RickP/MC5000_DevKit/gui/serialcommunication.h

#ifndef SERIALCOMMUNICATION_H
#define SERIALCOMMUNICATION_H

#include <QSerialPort>
#include <QTimer>
#include <QObject>
#include <QDebug>
#include <QMap>

class SerialCommunication : public QObject {
Q_OBJECT

Q_PROPERTY(int mcuConnections READ mcuConnections NOTIFY mcuConnectionChanged)
Q_PROPERTY(QStringList serialports READ serialports NOTIFY serialportsChanged)
Q_PROPERTY(QString errorMessage READ errorMessage NOTIFY errorMessageChanged)
Q_PROPERTY(QList<int> accRegisters READ accRegisters NOTIFY accRegistersChanged)
Q_PROPERTY(QList<int> datRegisters READ datRegisters NOTIFY datRegistersChanged)
Q_PROPERTY(QList<bool> isProgrammed READ isProgrammed NOTIFY isProgrammedChanged)

const QString LABEL_MARKER = ":";
const QString COMMENT_MARKER = "#";
const char LABEL_HEXCODE = 0x10 << 2;
const char START_CHAR = 0x7F;
const char END_CHAR = 0x7E;
const int SERIAL_DELAY = 8;
const int UPLOAD_RETRIES = 15;
const int MAX_PROGRAM_LENGTH = 74;

public:
explicit SerialCommunication(QObject *parent = nullptr);
~SerialCommunication();
int mcuConnections() const;
QStringList serialports();
QString errorMessage();
QList<int> datRegisters();
QList<int> accRegisters();
QList<bool> isProgrammed();

public slots:         // slots are public methods available in QML
void connectPort(QString port);
void updateRegisters();
void startUpload(QStringList codeList);
void loadPorts();
void readData();

signals:
void mcuConnectionChanged();
void errorMessageChanged();
void serialportsChanged();
void accRegistersChanged();
void datRegistersChanged();
void isProgrammedChanged();

private:
const int m_serialBaudRate = 19200;
QTimer *m_uploadTimeout;
QSerialPort *m_serial = nullptr;
int m_mcuConnections = 0;
int m_tries[3] = {0};
QString m_errorMessage = "";
QStringList m_serialports = {};
QStringList m_codeList = {};
QList<int> m_datRegisters = {0,0,0,0,0};
QList<int> m_accRegisters = {0,0,0,0,0};
QList<bool> m_isProgrammed = {false, false, false, false};
QList<bool> m_uploadDone = {true, true, true, true};
char encode8BitVal(QString);
char* encode16BitVal(QString);
void writeSerialByte(char, bool debug=false);
void upload(int mcuNum = 0);
void checkUpload();


const QMap<QString, char> registerEncodings = {
    {"x0", 0x40},
    {"x1", 0x48},
    {"p0", 0x50},
    {"p1", 0x58},
    {"dat", 0x60},
    {"acc", 0x70}
};

const QMap<QString, QPair<uint8_t, QStringList>> commands = {
    {
        "nop", {
            0x01 << 2, {}
        }
    },
    {
        "mov", {
            0x02 << 2, {"ri", "r"}
        }
    },
    {
        "jmp", {
            0x03 << 2, {"l"}
        },
    },
    {
        "slp", {
            0x04 << 2, {"ri"}
        },
    },
    {
        "slx", {
            0x05 << 2, {"r"}
        },
    },
    {
        "teq", {
            0x06 << 2, {"ri", "ri"}
        },
    },
    {
        "tgt", {
            0x07 << 2, {"ri", "ri"}
        },
    },
    {
        "tlt", {
            0x08 << 2, {"ri", "ri"}
        },
    },
    {
        "tcp", {
            0x09 << 2, {"ri", "ri"}
        },
    },
    {
        "add", {
            0x0A << 2, {"ri"}
        },
    },
    {
        "sub", {
            0x0B << 2, {"ri"}
        },
    },
    {
        "mul", {
            0x0C << 2, {"ri"}
        },
    },
    {
        "not", {
            0x0D << 2, {}
        }
    },
    {
        "dgt", {
            0x0E << 2, {"ri"}
        },
    },
    {
        "dst", {
            0x0F << 2, {"ri", "ri"}
        },
    }
};


};


#endif // SERIALCOMMUNICATION_H
